LeonardoDG2084/arduinoPorscheWheel/imgs/IMG_20250106_212807.jpg

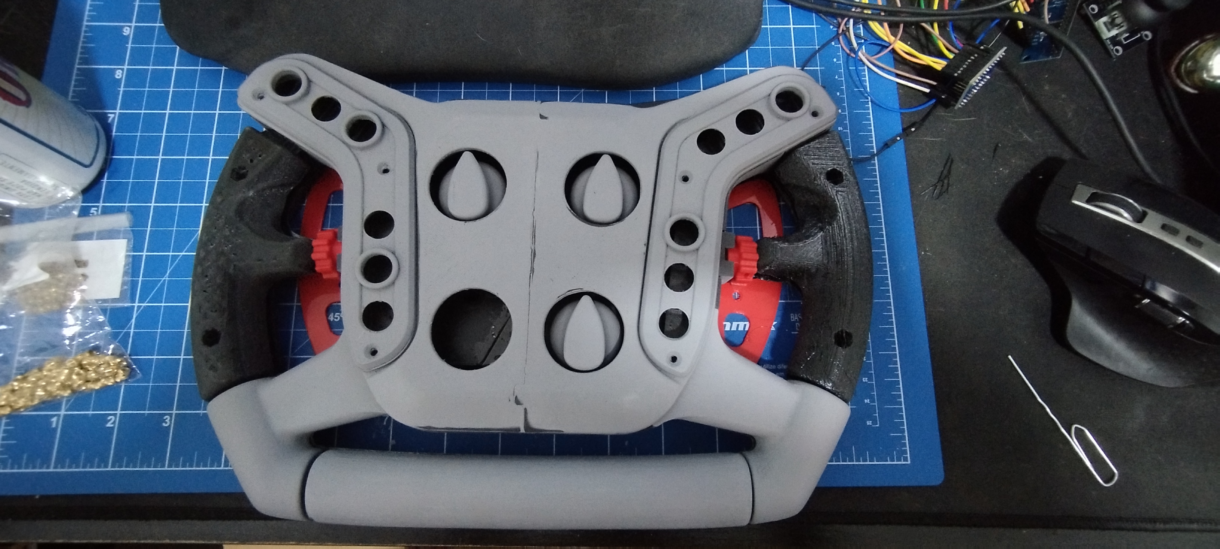
imgs/IMG_20250106_212807.jpg
