LeonardoDG2084/arduinoPorscheWheel/imgs/IMG_20250107_203819.jpg

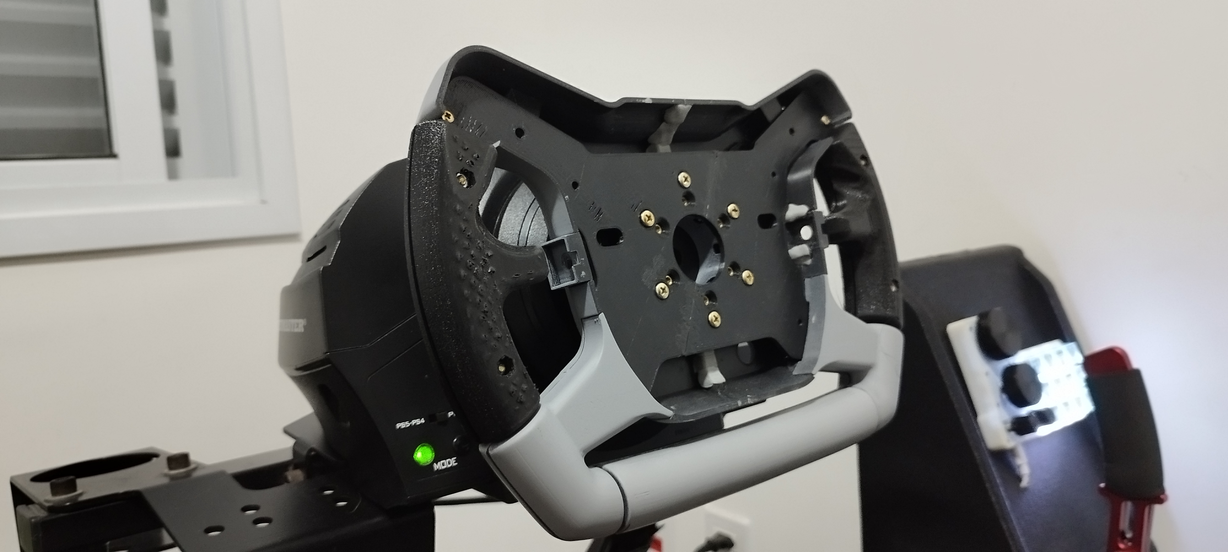
imgs/IMG_20250107_203819.jpg
