LeonardoDG2084/arduinoPorscheWheel/imgs/IMG_20250108_160758.jpg

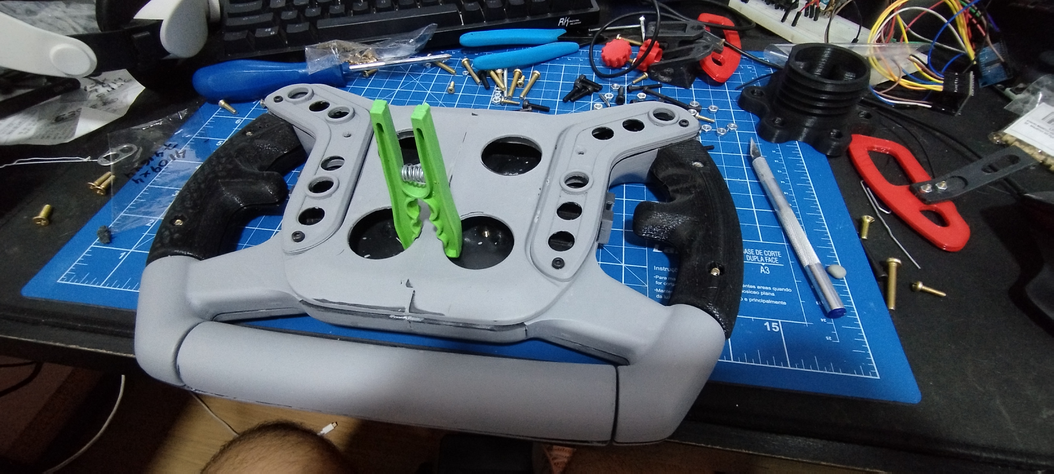
imgs/IMG_20250108_160758.jpg
