LeonardoDG2084/arduinoPorscheWheel/imgs/IMG_20250111_082540.jpg

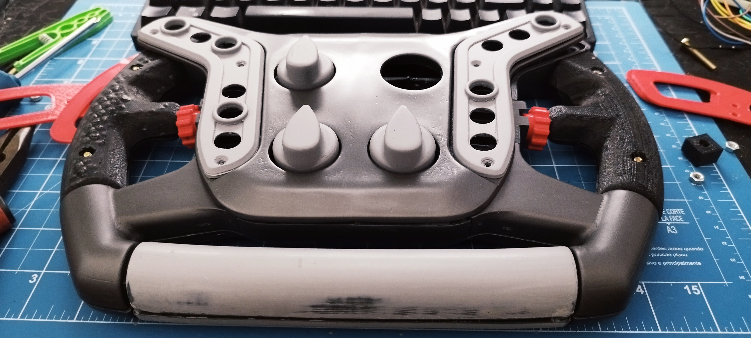
imgs/IMG_20250111_082540.jpg
