LeonardoDG2084/arduinoPorscheWheel/imgs/IMG_20250124_190212.jpg

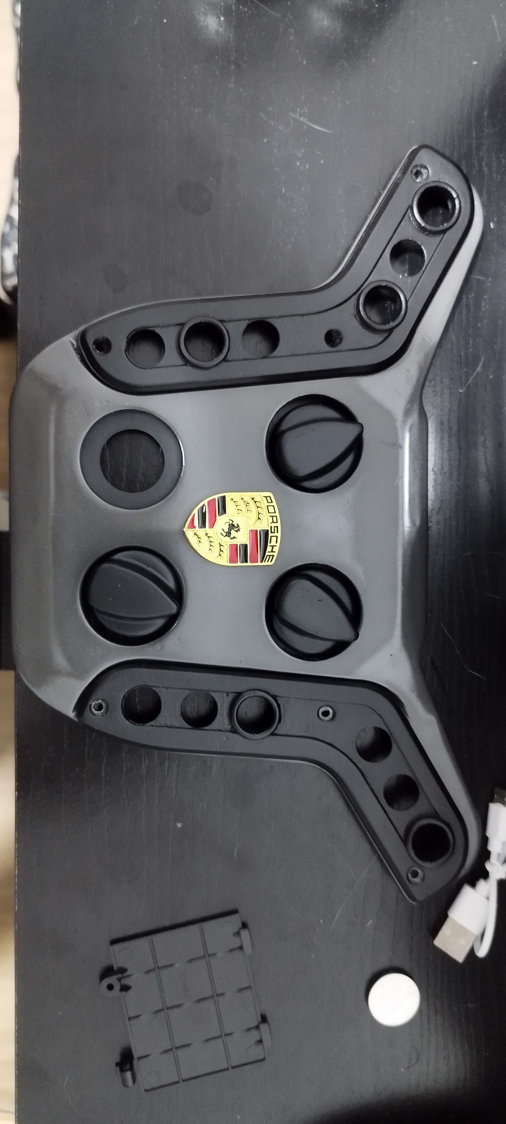
imgs/IMG_20250124_190212.jpg
