LeonardoDG2084/arduinoPorscheWheel/imgs/IMG_20250125_171732.jpg

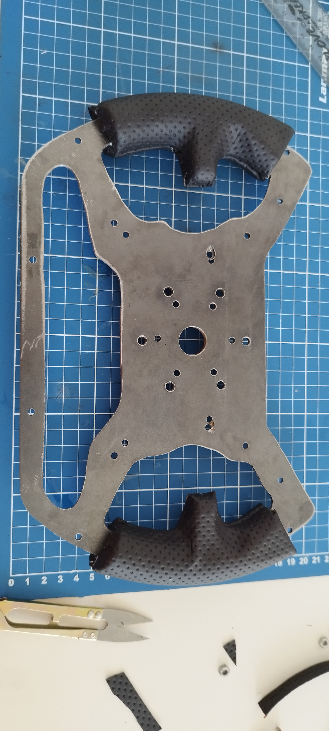
imgs/IMG_20250125_171732.jpg
