LeonardoDG2084/arduinoPorscheWheel/imgs/IMG_20250125_175444.jpg

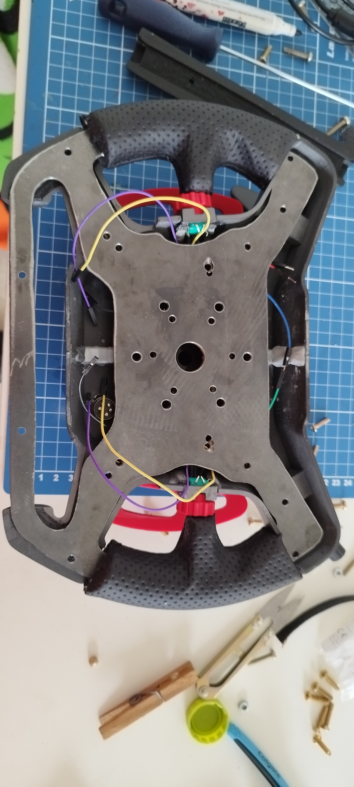
imgs/IMG_20250125_175444.jpg
