LeonardoDG2084/arduinoPorscheWheel/imgs/IMG_20250125_180240.jpg

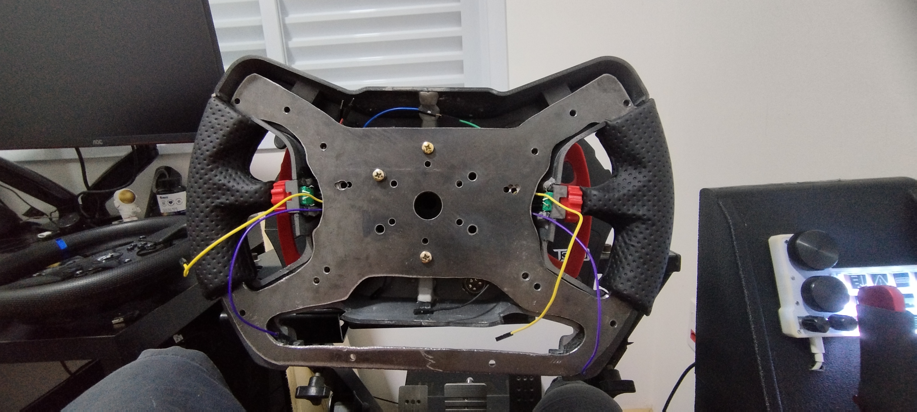
imgs/IMG_20250125_180240.jpg
