LeonardoDG2084/arduinoPorscheWheel/imgs/IMG_20250126_211610.jpg

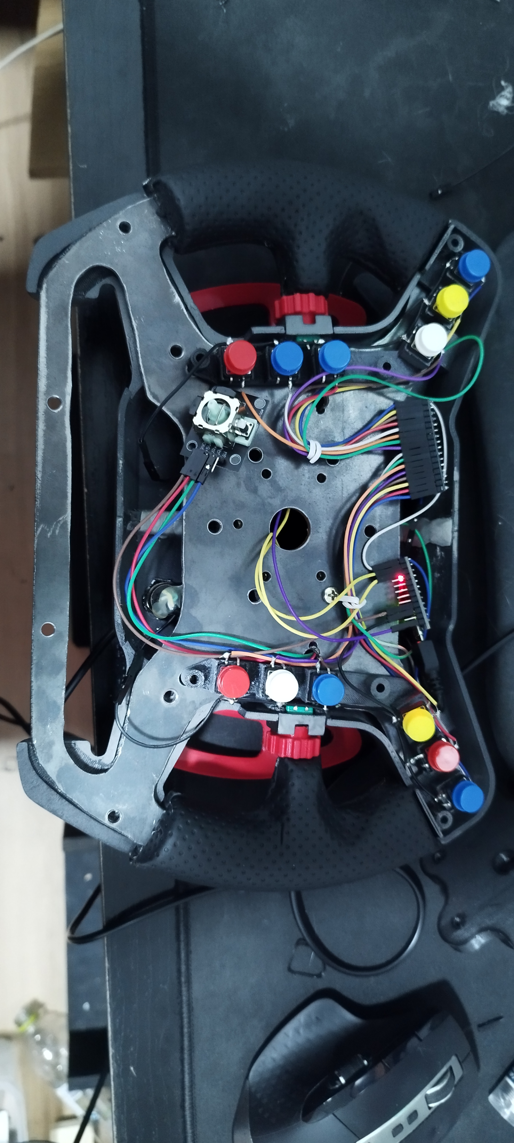
imgs/IMG_20250126_211610.jpg
