LeonardoDG2084/arduinoPorscheWheel/imgs/IMG_20250206_072802.jpg

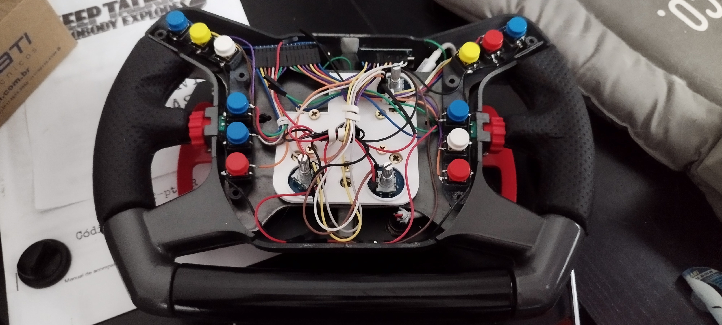
imgs/IMG_20250206_072802.jpg
