LeonardoDG2084/arduinoPorscheWheel/imgs/IMG_20250703_170919.jpg

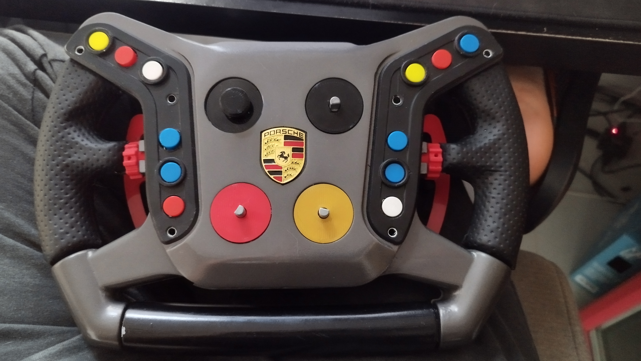
imgs/IMG_20250703_170919.jpg
