LeonardoDG2084/arduinoPorscheWheel/imgs/IMG_20250706_102237.jpg

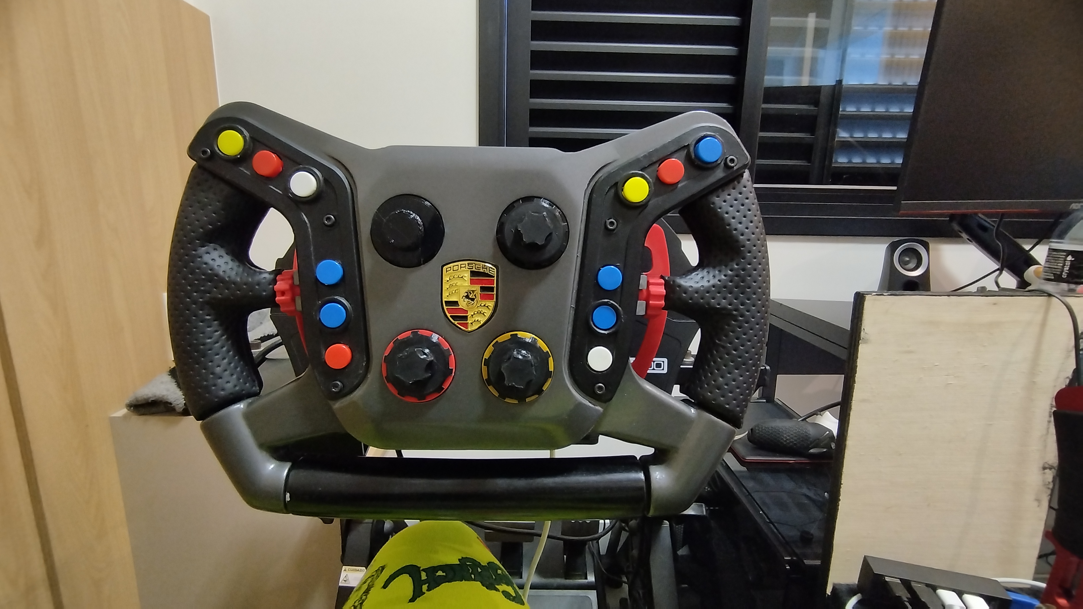
imgs/IMG_20250706_102237.jpg
