LeonardoDG2084/arduinoPorscheWheel/render-oficial/Back Render.JPG

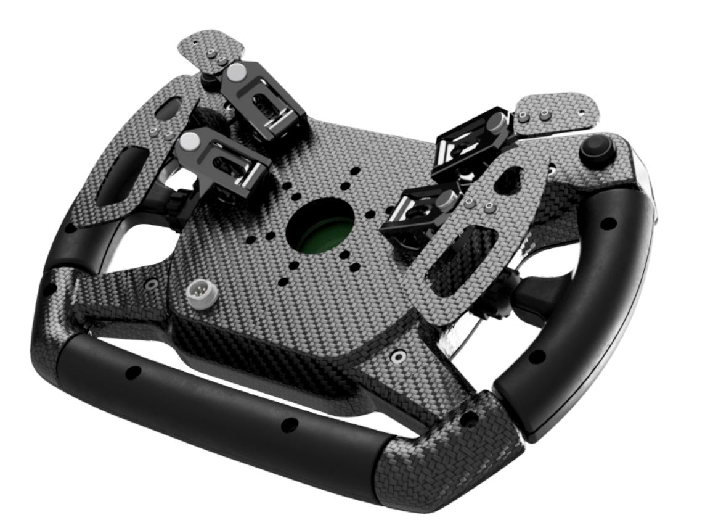
render-oficial/Back Render.JPG
