LeonardoDG2084/arduinoPorscheWheel/render-oficial/Front Render.JPG

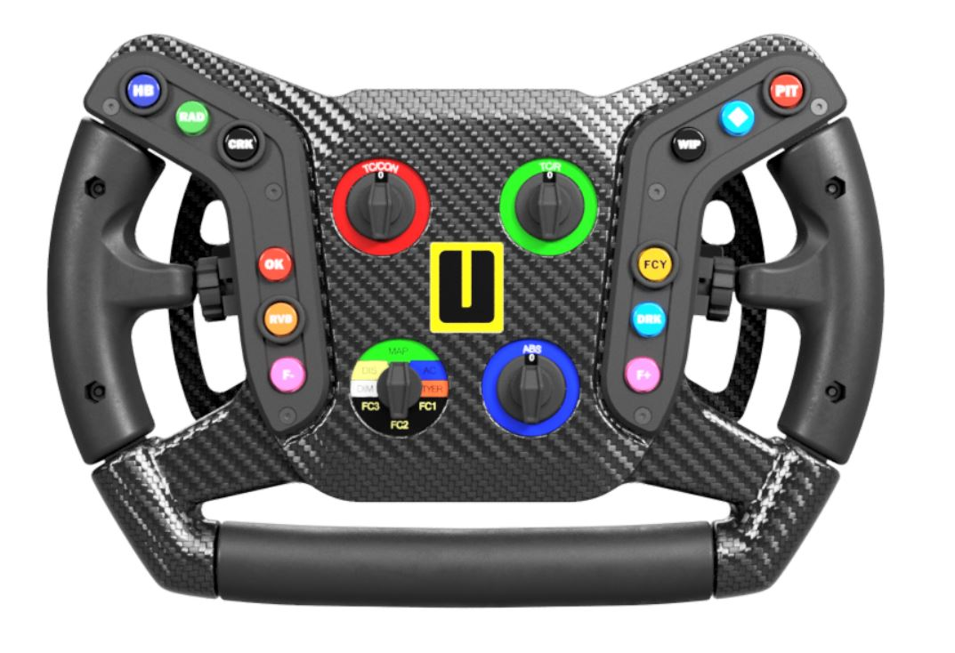
render-oficial/Front Render.JPG
