LeonardoDG2084/arduinoPorscheWheel/render-oficial/Side Render.JPG

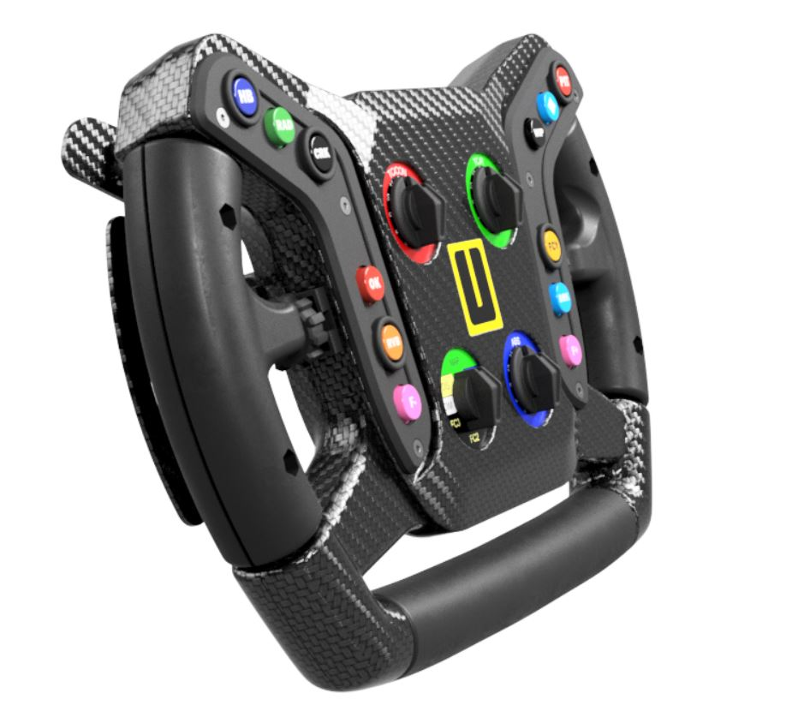
render-oficial/Side Render.JPG
