LeonardoDG2084/arduinoPorscheWheel/Turn 911 GT3 R 2023 DIY Files/Shifters/CNC/Treaded.JPG

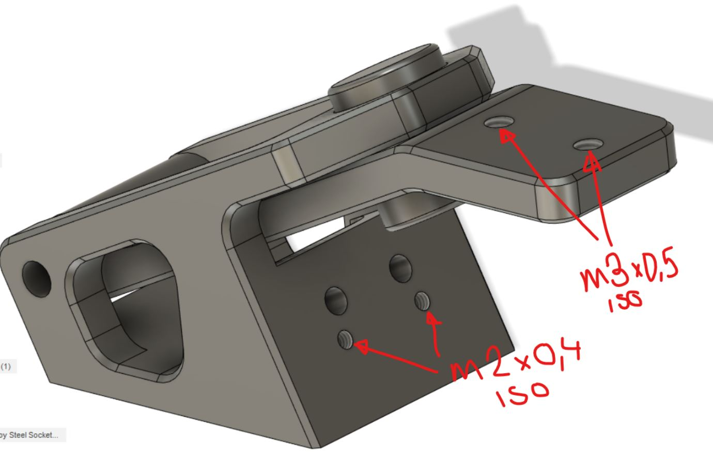
Turn 911 GT3 R 2023 DIY Files/Shifters/CNC/Treaded.JPG
