LeonardoDG2084/arduinoPorscheWheel/custom/top-knobs-and-joystick.stl

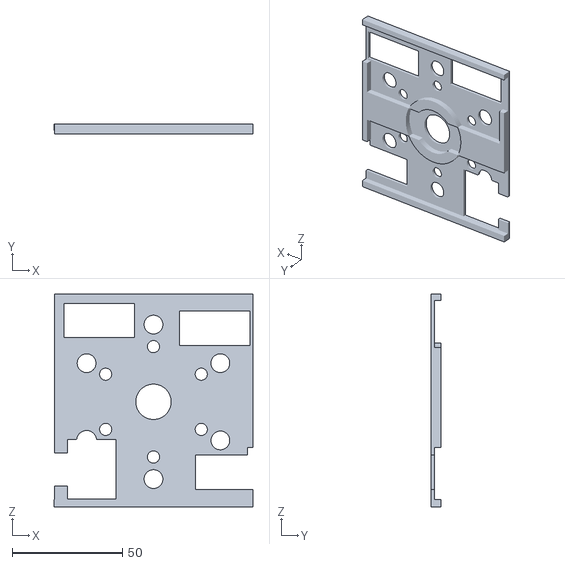
[picture p34: CAD file, 2025-07-14]
custom/top-knobs-and-joystick.stl
90.0 x 4.50 x 96.5
