LeonardoDG2084/arduinoPorscheWheel/Turn 911 GT3 R 2023 DIY Files/3D Pritning/3D Printing Service/PA-12 Nylon/Handel Mid Front MJF.stl

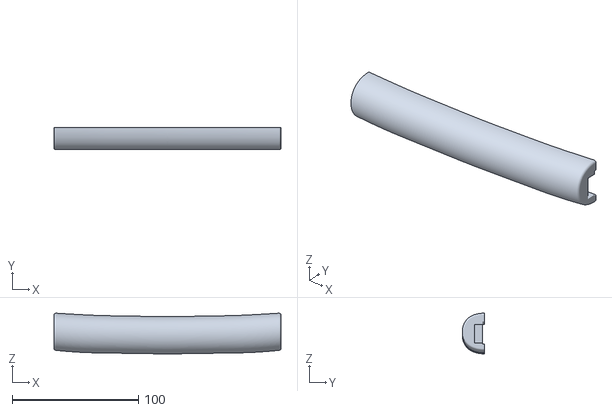
[picture p35: CAD file, 2025-07-14]
Turn 911 GT3 R 2023 DIY Files/3D Pritning/3D Printing Service/PA-12 Nylon/Handel Mid Front MJF.stl
180.0 x 17.8 x 32.3
