LeonardoDG2084/arduinoPorscheWheel/Turn 911 GT3 R 2023 DIY Files/3D Pritning/3D Printing Service/Resin Black/Thumb Rotor.stl

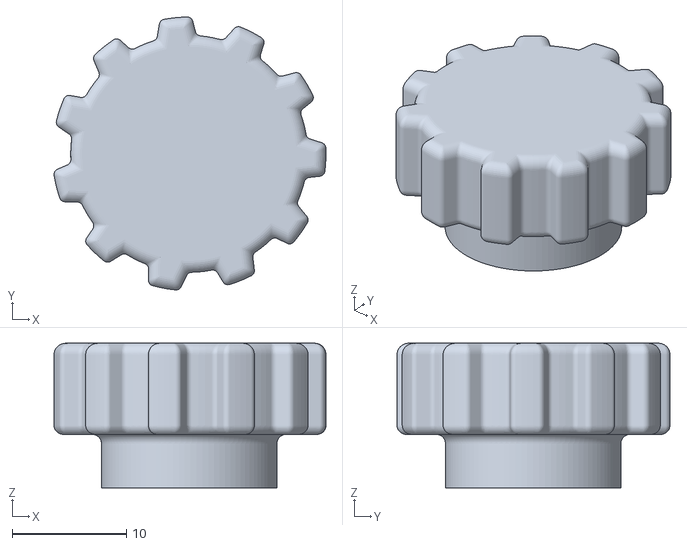
[picture p36: CAD file, 2025-07-14]
Turn 911 GT3 R 2023 DIY Files/3D Pritning/3D Printing Service/Resin Black/Thumb Rotor.stl
23.9 x 23.9 x 12.7
