LeonardoDG2084/arduinoPorscheWheel/Turn 911 GT3 R 2023 DIY Files/3D Pritning/FDM Pritning/PCB holder Right.stl

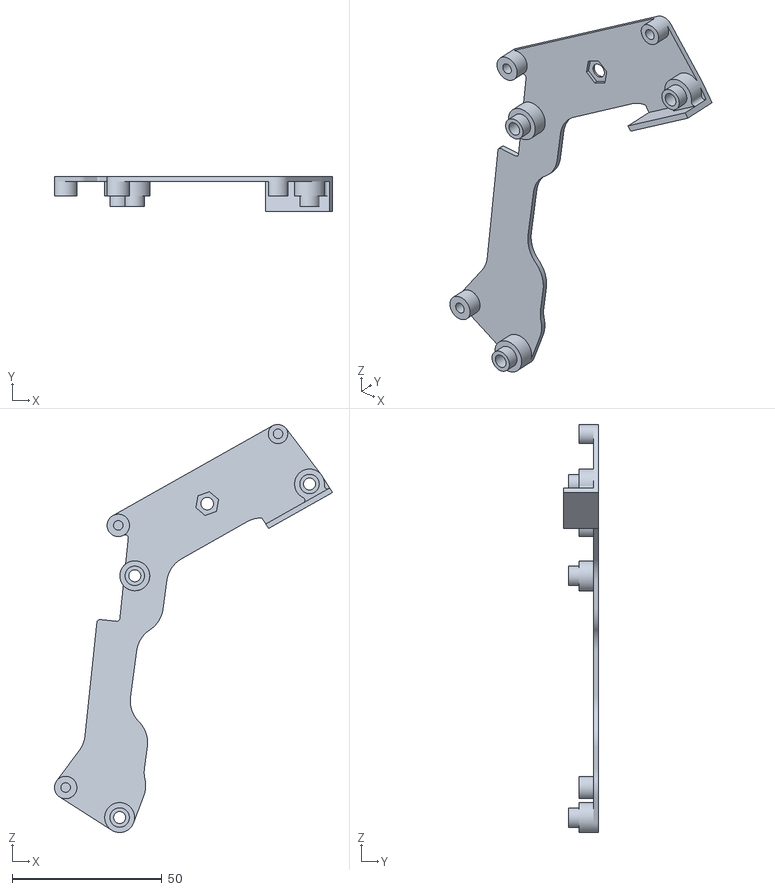
[picture p37: CAD file, 2025-07-14]
Turn 911 GT3 R 2023 DIY Files/3D Pritning/FDM Pritning/PCB holder Right.stl
92.9 x 11.6 x 136.3
