LeonardoDG2084/arduinoPorscheWheel/Turn 911 GT3 R 2023 DIY Files/Acrylic Sheet/Acrylic sheet CAD.step

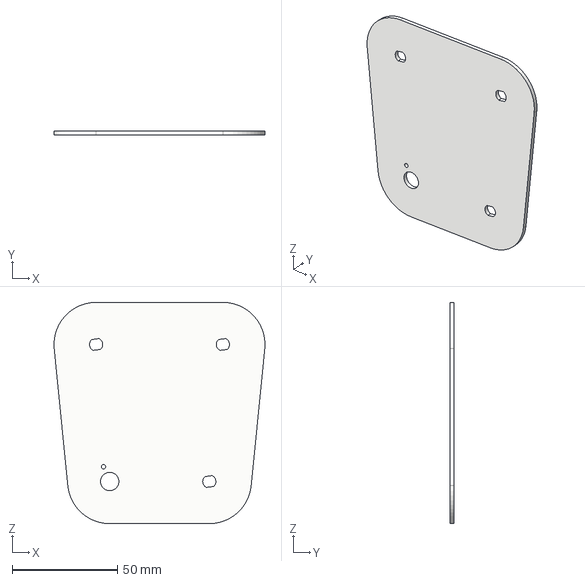
[picture p38: CAD file, 2025-07-14]
Turn 911 GT3 R 2023 DIY Files/Acrylic Sheet/Acrylic sheet CAD.step
100.2 x 2.00 x 105.1 mm
