LeonardoDG2084/arduinoPorscheWheel/Turn 911 GT3 R 2023 DIY Files/Core Plate and Shifters/Small Shifter plate .step

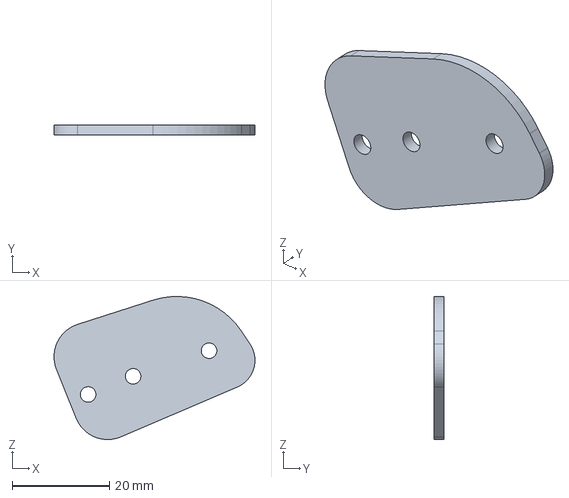
[picture p39: CAD file, 2025-07-14]
Turn 911 GT3 R 2023 DIY Files/Core Plate and Shifters/Small Shifter plate .step
41.4 x 2.00 x 29.5 mm
