LeonardoDG2084/arduinoPorscheWheel/Turn 911 GT3 R 2023 DIY Files/Grips/Insert Grips Softtuch/Left Back grip Inserts Softtuch.stl

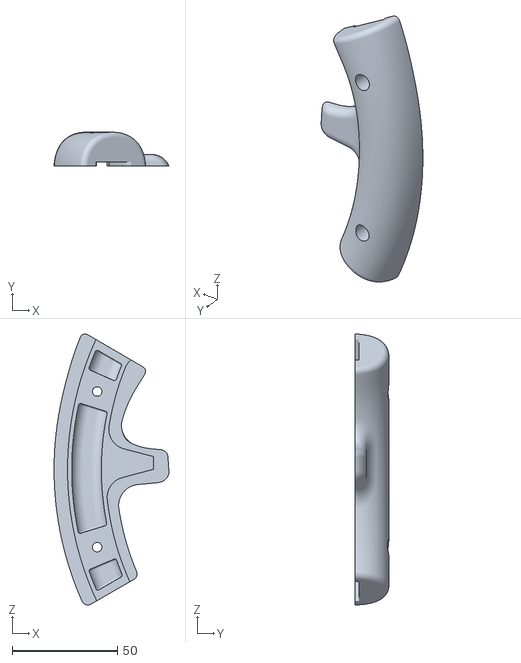
[picture p40: CAD file, 2025-07-14]
Turn 911 GT3 R 2023 DIY Files/Grips/Insert Grips Softtuch/Left Back grip Inserts Softtuch.stl
54.6 x 16.0 x 128.8
