LeonardoDG2084/arduinoPorscheWheel/Turn 911 GT3 R 2023 DIY Files/Grips/Molded Grips/RB Mold.stl

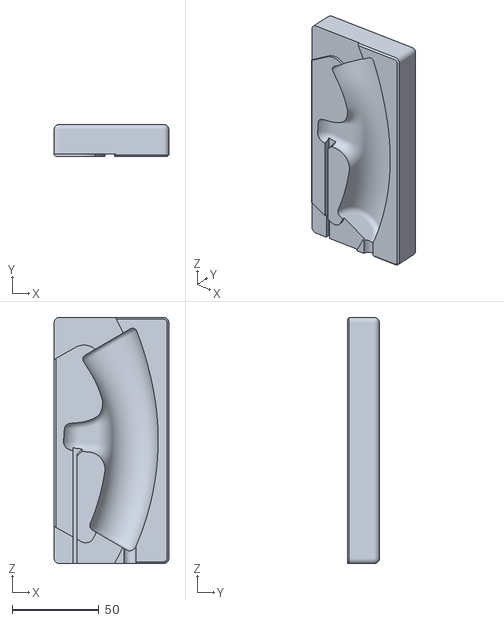
[picture p41: CAD file, 2025-07-14]
Turn 911 GT3 R 2023 DIY Files/Grips/Molded Grips/RB Mold.stl
66.3 x 18.5 x 142.1
