LeonardoDG2084/arduinoPorscheWheel/Turn 911 GT3 R 2023 DIY Files/Grips/Printed No Cap/Grip NoGap Right Front.stl

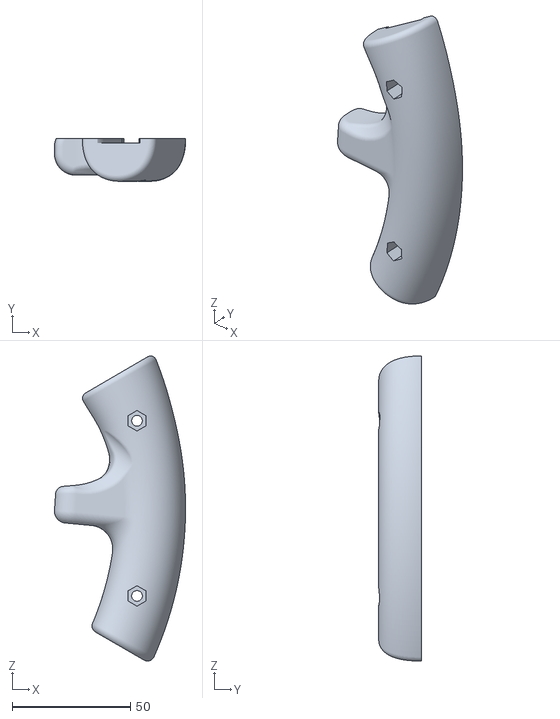
[picture p42: CAD file, 2025-07-14]
Turn 911 GT3 R 2023 DIY Files/Grips/Printed No Cap/Grip NoGap Right Front.stl
55.4 x 18.0 x 128.8
