LeonardoDG2084/arduinoPorscheWheel/Turn 911 GT3 R 2023 DIY Files/Shifters/3D Pritning/Shifter Lever v2_4p.stl

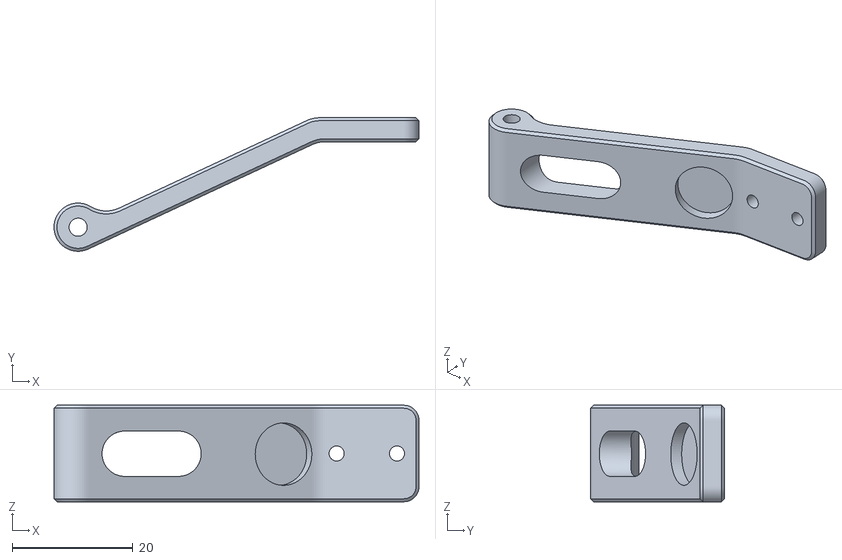
[picture p43: CAD file, 2025-07-14]
Turn 911 GT3 R 2023 DIY Files/Shifters/3D Pritning/Shifter Lever v2_4p.stl
60.5 x 22.1 x 16.0
