LeonardoDG2084/arduinoPorscheWheel/Turn 911 GT3 R 2023 DIY Files/Shifters/CNC/Turn 992 GT3 R DIY Sifter.step

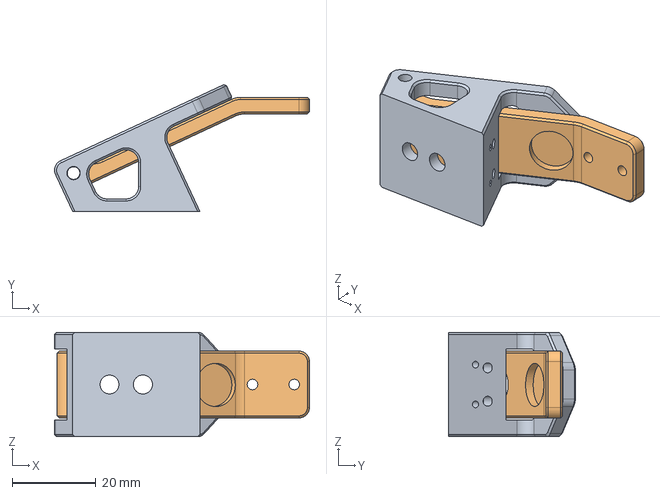
[picture p44: CAD file, 2025-07-14]
Turn 911 GT3 R 2023 DIY Files/Shifters/CNC/Turn 992 GT3 R DIY Sifter.step
61.1 x 30.3 x 25.0 mm
