LeonardoDG2084/arduinoPorscheWheel/custom/base-analogico.3mf

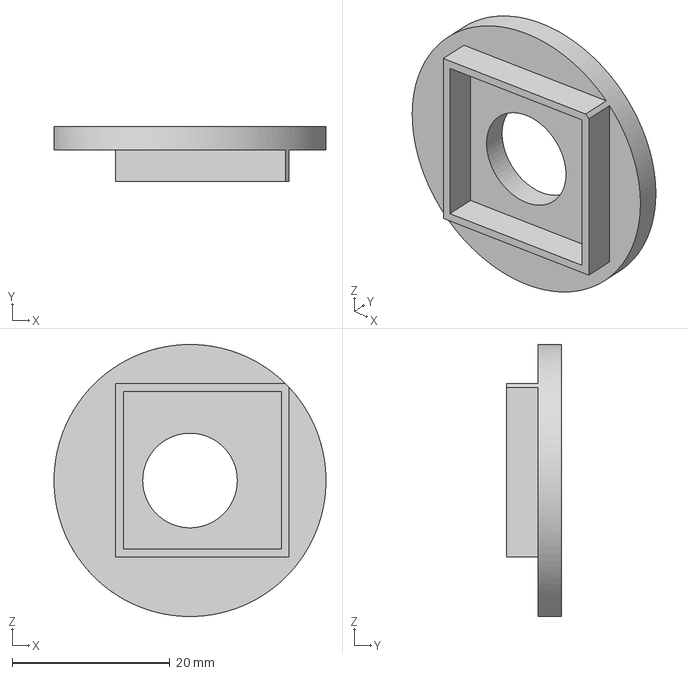
[picture p45: CAD file, 2025-07-14]
custom/base-analogico.3mf
34.5 x 7.00 x 34.5 mm
