LeonardoDG2084/arduinoPorscheWheel/Turn 911 GT3 R 2023 DIY Files/3D Pritning/3D Printing Service/Resin Black/6p Rotor Knob.stl

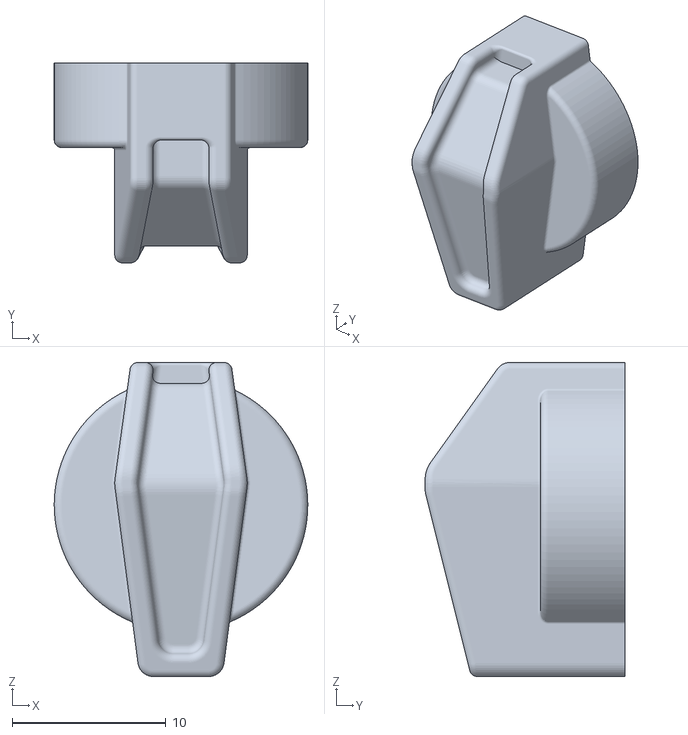
[picture p46: CAD file, 2025-07-14]
Turn 911 GT3 R 2023 DIY Files/3D Pritning/3D Printing Service/Resin Black/6p Rotor Knob.stl
16.5 x 13.0 x 20.4
