LeonardoDG2084/arduinoPorscheWheel/Turn 911 GT3 R 2023 DIY Files/3D Pritning/FDM Pritning/Handel Front Mid.stl

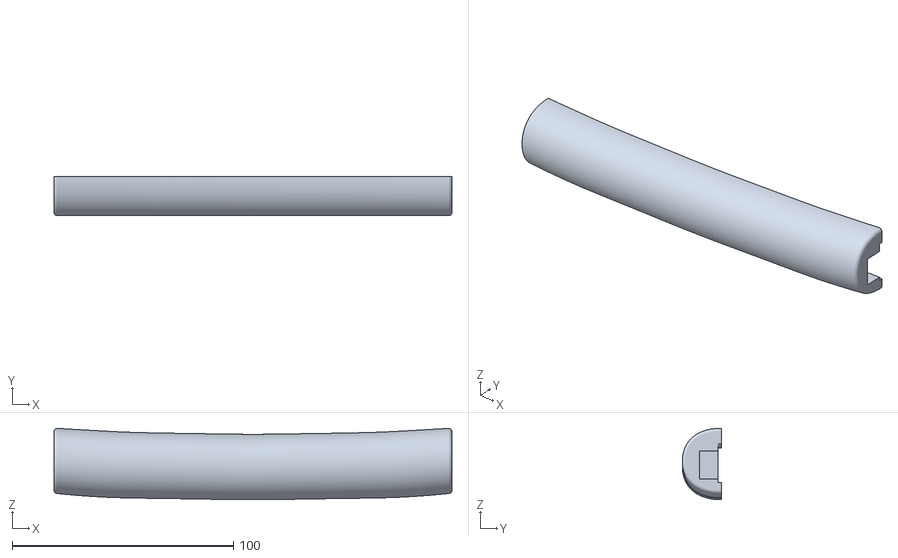
[picture p47: CAD file, 2025-07-14]
Turn 911 GT3 R 2023 DIY Files/3D Pritning/FDM Pritning/Handel Front Mid.stl
180.0 x 17.8 x 32.3
