LeonardoDG2084/arduinoPorscheWheel/Turn 911 GT3 R 2023 DIY Files/Core Plate and Shifters/Big Shifter Plate.dxf

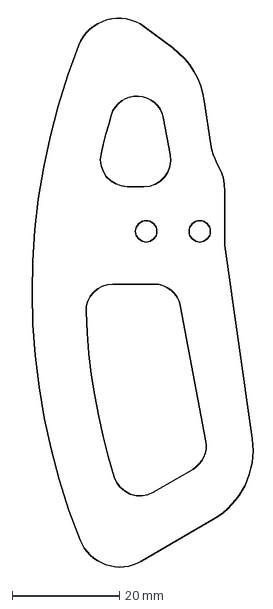
[picture p48: CAD file, 2025-07-14]
Turn 911 GT3 R 2023 DIY Files/Core Plate and Shifters/Big Shifter Plate.dxf
44.9 x 103.1 mm
