LeonardoDG2084/arduinoPorscheWheel/Turn 911 GT3 R 2023 DIY Files/Grips/Printed Gap/Grip Gap Left Back.stl

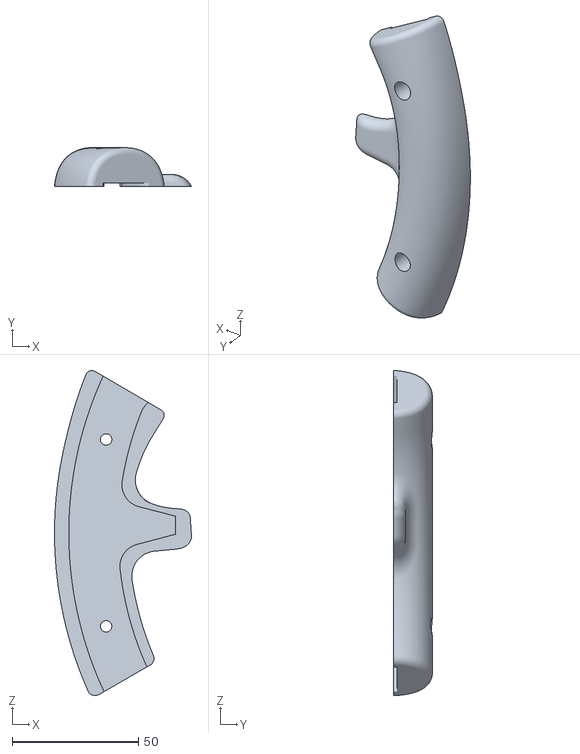
[picture p49: CAD file, 2025-07-14]
Turn 911 GT3 R 2023 DIY Files/Grips/Printed Gap/Grip Gap Left Back.stl
54.3 x 15.3 x 128.7
