LeonardoDG2084/arduinoPorscheWheel/custom/knob-base.stl

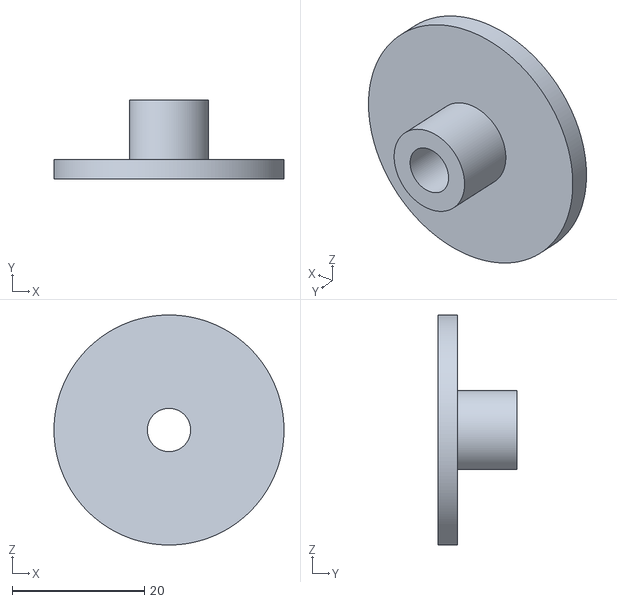
[picture p50: CAD file, 2025-07-14]
custom/knob-base.stl
34.8 x 12.0 x 34.8
