LeonardoDG2084/arduinoPorscheWheel/Turn 911 GT3 R 2023 DIY Files/3D Pritning/3D Printing Service/PA-12 Nylon/Front Lid MJF.stl

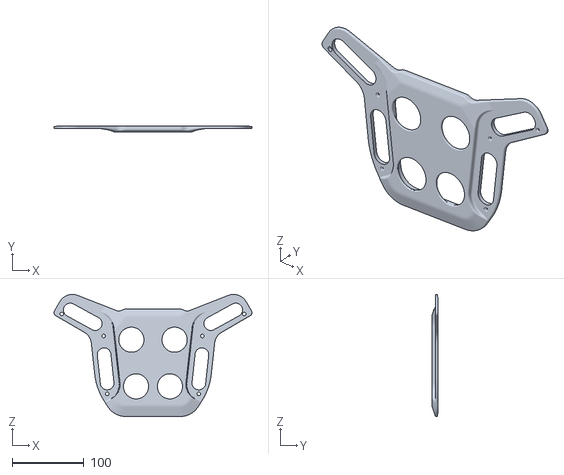
[picture p51: CAD file, 2025-07-14]
Turn 911 GT3 R 2023 DIY Files/3D Pritning/3D Printing Service/PA-12 Nylon/Front Lid MJF.stl
276.2 x 9.00 x 170.3
