LeonardoDG2084/arduinoPorscheWheel/Turn 911 GT3 R 2023 DIY Files/3D Pritning/FDM Pritning/Handel Front Right.stl

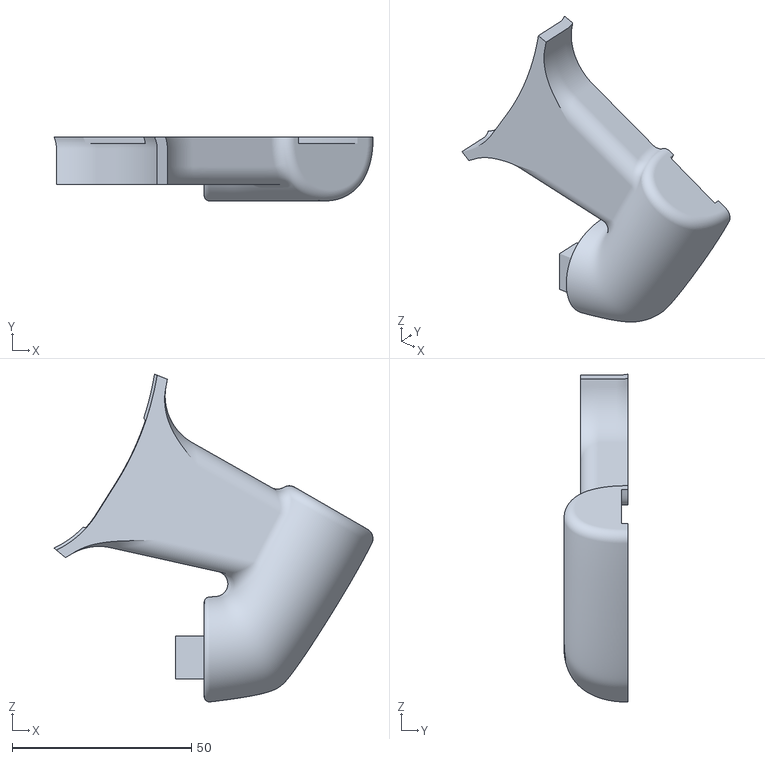
[picture p52: CAD file, 2025-07-14]
Turn 911 GT3 R 2023 DIY Files/3D Pritning/FDM Pritning/Handel Front Right.stl
89.1 x 17.8 x 91.6
