LeonardoDG2084/arduinoPorscheWheel/custom/base-knobs-and-joysticks.stl

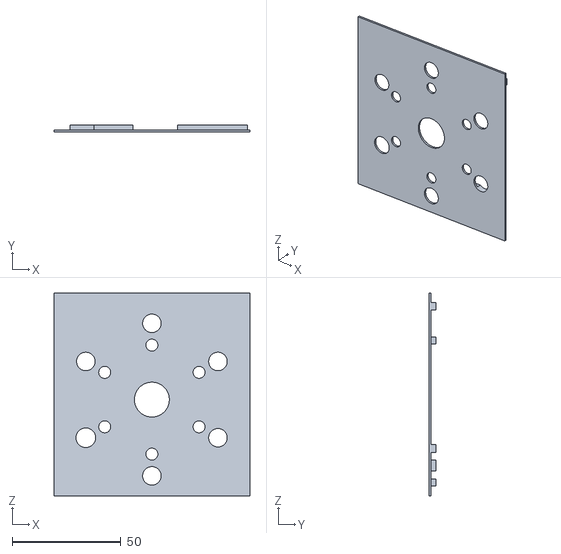
[picture p53: CAD file, 2025-07-14]
custom/base-knobs-and-joysticks.stl
89.9 x 3.20 x 93.0
