LeonardoDG2084/arduinoPorscheWheel/Turn 911 GT3 R 2023 DIY Files/3D Pritning/3D Printing Service/Resin Black/Thumb Encoder Holder v2 Right.stl

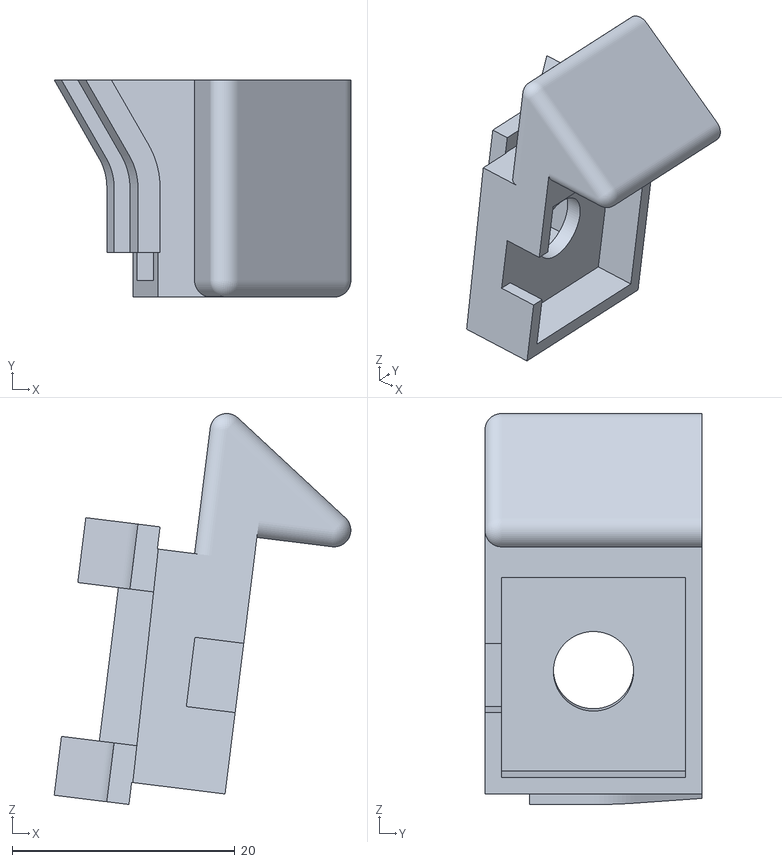
[picture p55: CAD file, 2025-07-14]
Turn 911 GT3 R 2023 DIY Files/3D Pritning/3D Printing Service/Resin Black/Thumb Encoder Holder v2 Right.stl
26.6 x 19.5 x 35.1
