LeonardoDG2084/arduinoPorscheWheel/Turn 911 GT3 R 2023 DIY Files/3D Pritning/FDM Pritning/Front Lid Right.stl

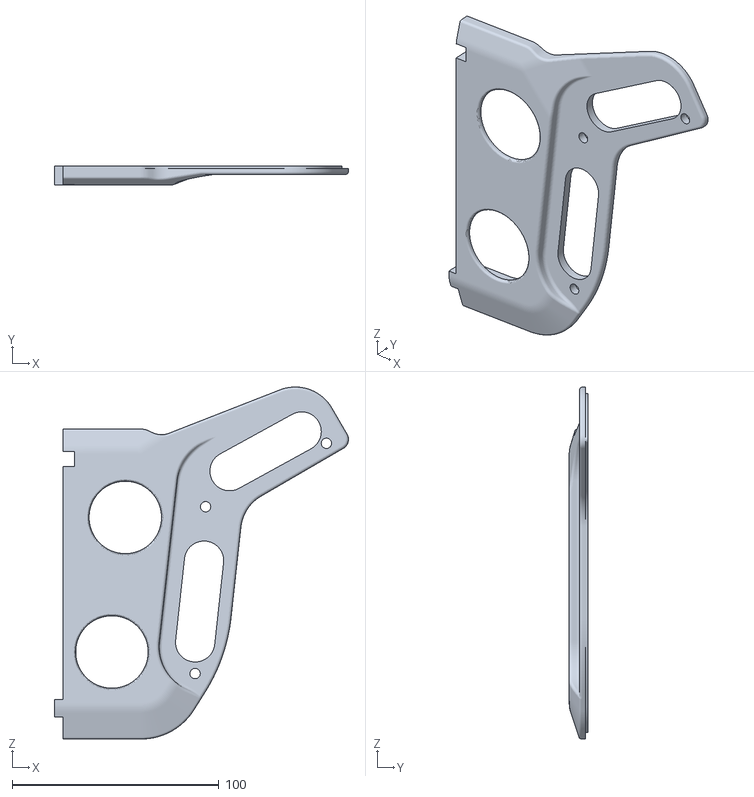
[picture p56: CAD file, 2025-07-14]
Turn 911 GT3 R 2023 DIY Files/3D Pritning/FDM Pritning/Front Lid Right.stl
142.2 x 9.00 x 170.3
