LeonardoDG2084/arduinoPorscheWheel/Turn 911 GT3 R 2023 DIY Files/Grips/Molded Grips/Mold Step.step

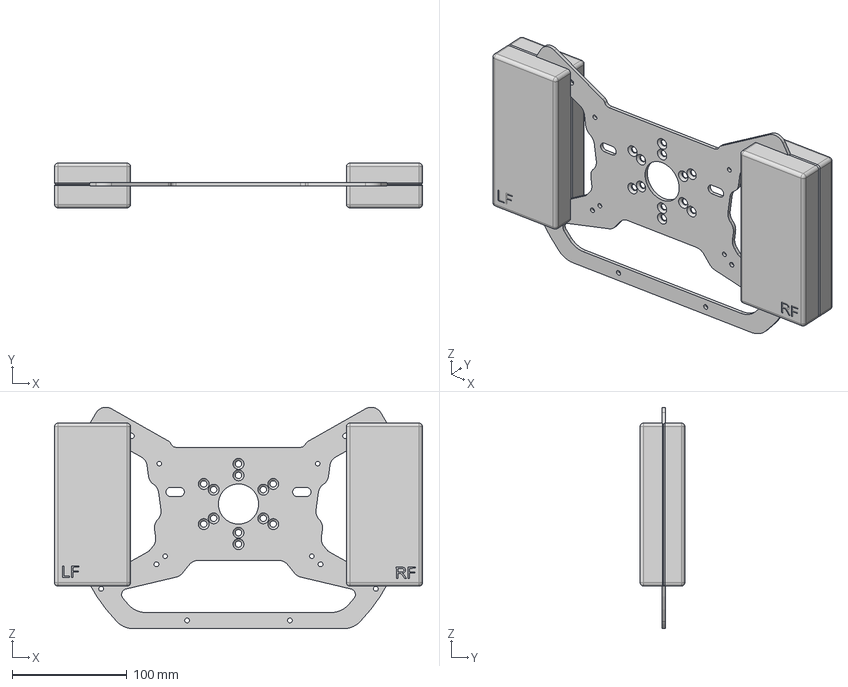
[picture p57: CAD file, 2025-07-14]
Turn 911 GT3 R 2023 DIY Files/Grips/Molded Grips/Mold Step.step
320.9 x 39.0 x 193.0 mm
LEFT Grip
RF Mold
RB Mold
LB Mold
LF Mold
RIGHT Grip
Main Plate
