LeonardoDG2084/arduinoPorscheWheel/custom/button-guard-ight.stl

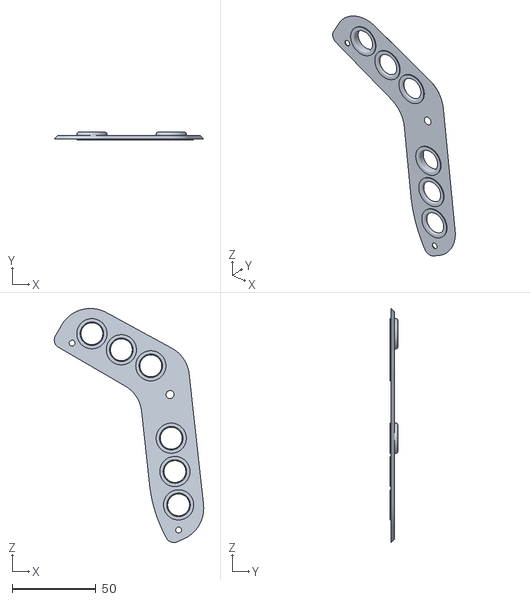
[picture p58: CAD file, 2025-07-14]
custom/button-guard-ight.stl
89.1 x 4.50 x 139.5
