LeonardoDG2084/arduinoPorscheWheel/Turn 911 GT3 R 2023 DIY Files/3D Pritning/3D Printing Service/Resin Black/Thumb Encoder Holder Right.stl

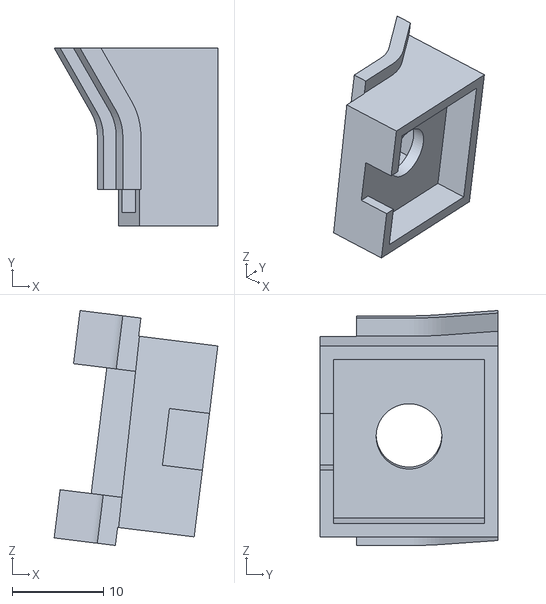
[picture p59: CAD file, 2025-07-14]
Turn 911 GT3 R 2023 DIY Files/3D Pritning/3D Printing Service/Resin Black/Thumb Encoder Holder Right.stl
17.9 x 19.5 x 25.8
