LeonardoDG2084/arduinoPorscheWheel/Turn 911 GT3 R 2023 DIY Files/3D Pritning/FDM Pritning/Handel Back Mid.stl

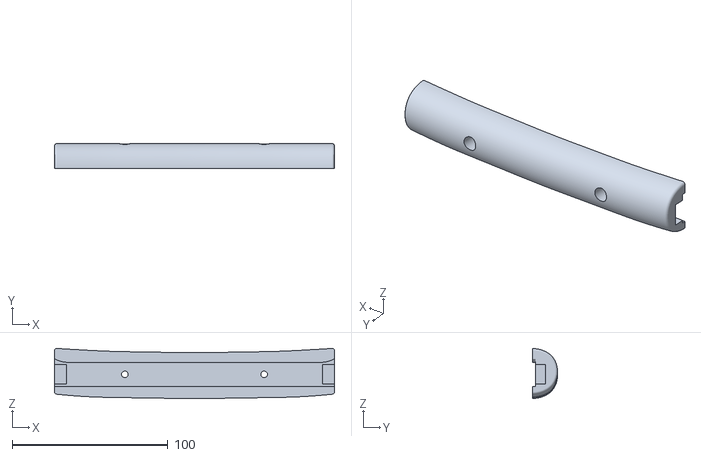
[picture p60: CAD file, 2025-07-14]
Turn 911 GT3 R 2023 DIY Files/3D Pritning/FDM Pritning/Handel Back Mid.stl
180.0 x 16.1 x 32.2
