LeonardoDG2084/arduinoPorscheWheel/custom/Knob.stl

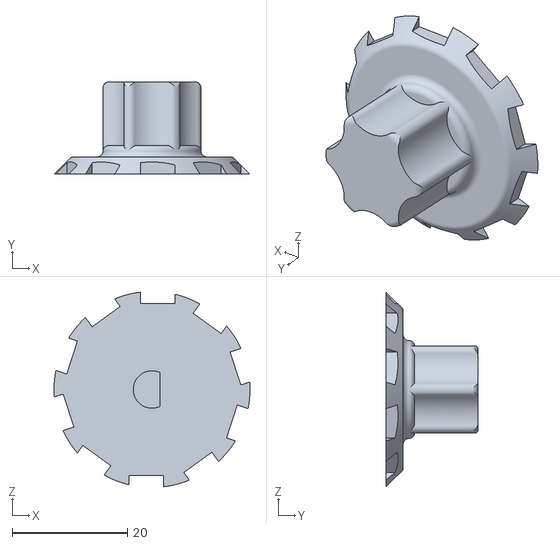
[picture p61: CAD file, 2025-07-14]
custom/Knob.stl
34.0 x 16.0 x 33.8
