LeonardoDG2084/arduinoPorscheWheel/Turn 911 GT3 R 2023 DIY Files/3D Pritning/3D Printing Service/Resin Black/12p Rotor Knob.stl

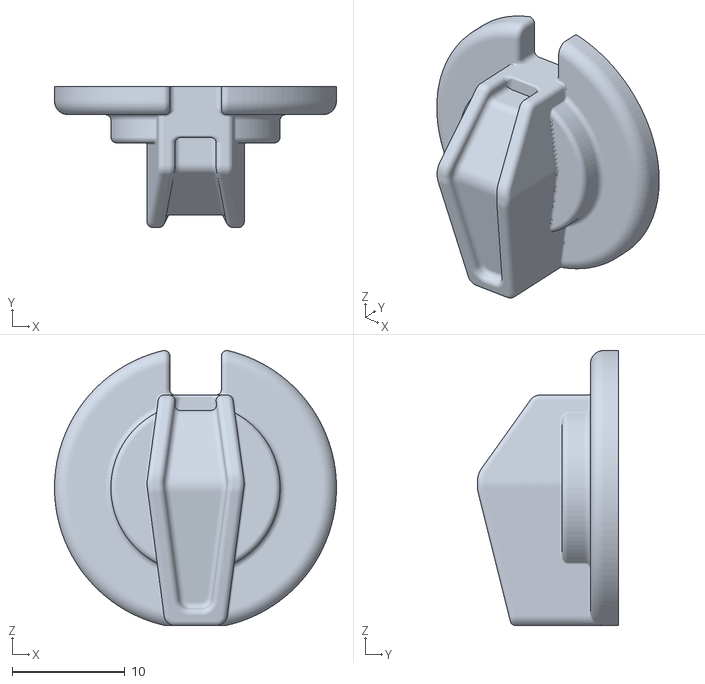
[picture p62: CAD file, 2025-07-14]
Turn 911 GT3 R 2023 DIY Files/3D Pritning/3D Printing Service/Resin Black/12p Rotor Knob.stl
25.0 x 12.5 x 24.4
