LeonardoDG2084/arduinoPorscheWheel/custom/thumbstick.stl

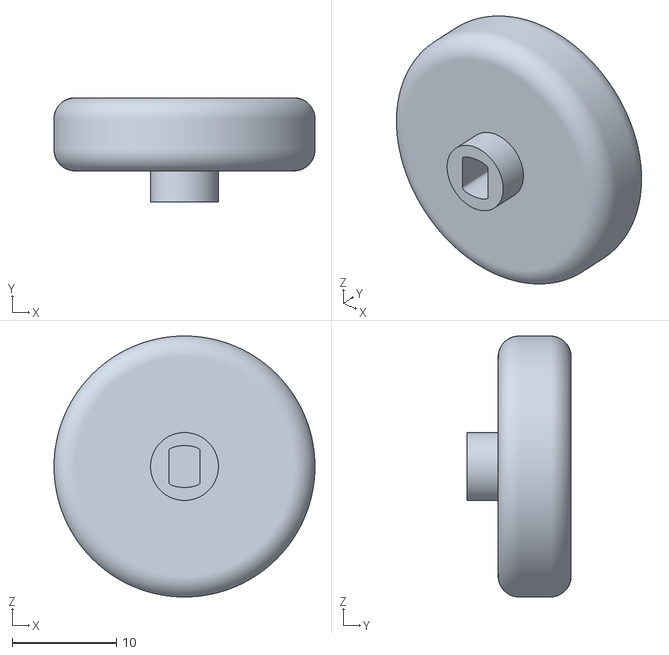
[picture p63: CAD file, 2025-07-14]
custom/thumbstick.stl
25.0 x 10.0 x 25.0
