LeonardoDG2084/arduinoPorscheWheel/custom/shifter-plate.stl

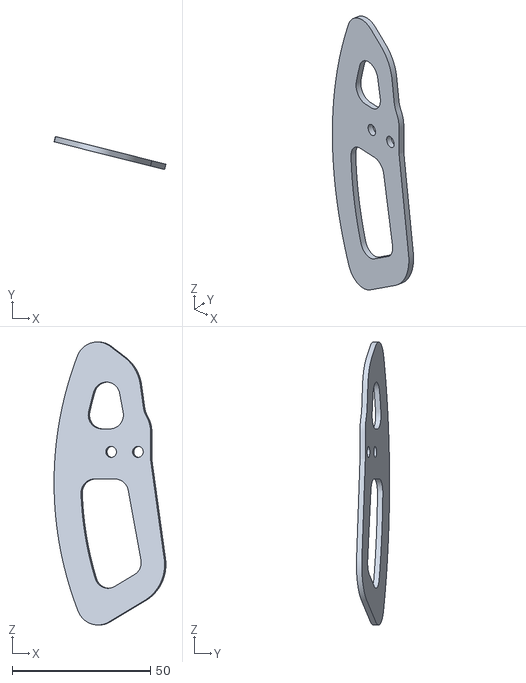
[picture p65: CAD file, 2025-07-14]
custom/shifter-plate.stl
40.5 x 12.0 x 102.4
