LeonardoDG2084/arduinoPorscheWheel/Turn 911 GT3 R 2023 DIY Files/PCB manufacturing/Page 2 Config JLC.PNG

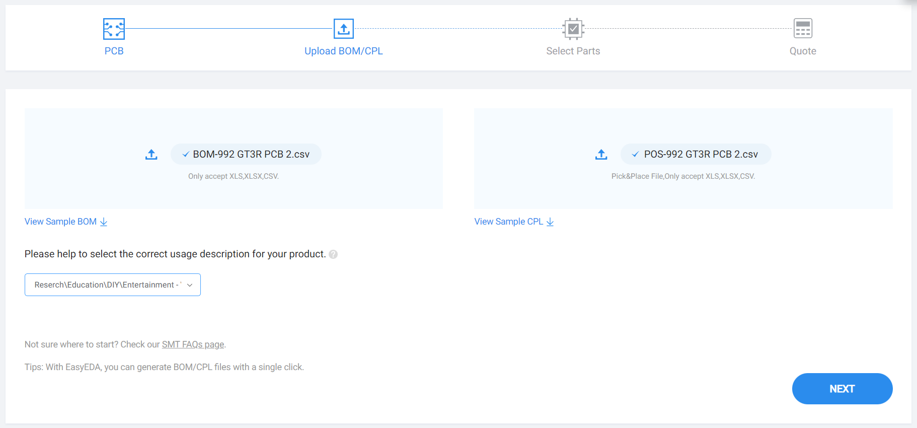
Turn 911 GT3 R 2023 DIY Files/PCB manufacturing/Page 2 Config JLC.PNG
